Jonathan-0101/skeletonKey/Hardware/Symbols_Footprints_3D_Models/3D Models/DMG3415UQ-7.stp

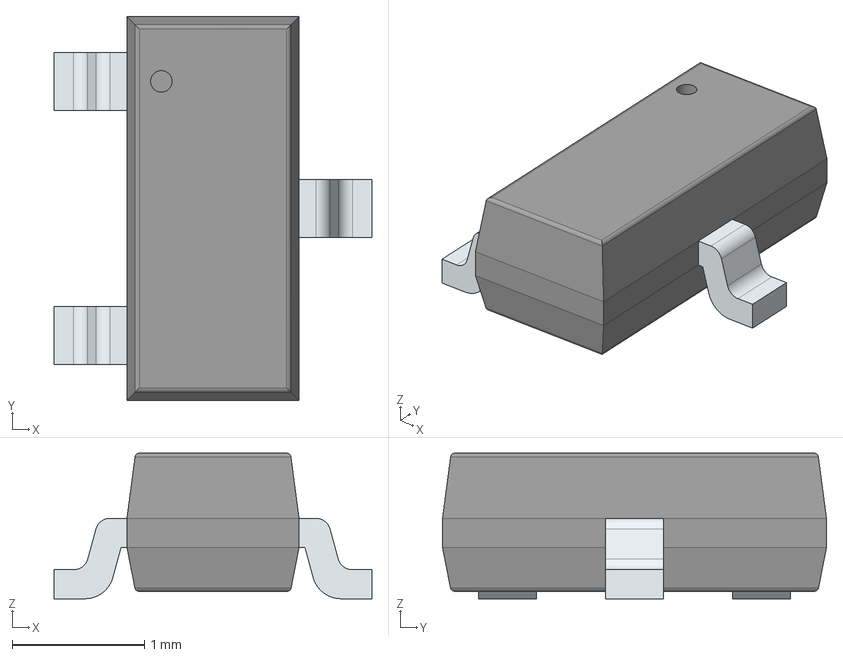
[picture p17: CAD file, 2025-07-19]
Hardware/Symbols_Footprints_3D_Models/3D Models/DMG3415UQ-7.stp
2.40 x 2.90 x 1.10 mm
PinsArrayL
FilletPinR
