Jonathan-0101/skeletonKey/Hardware/Symbols_Footprints_3D_Models/3D Models/C8051F330-GM.stp

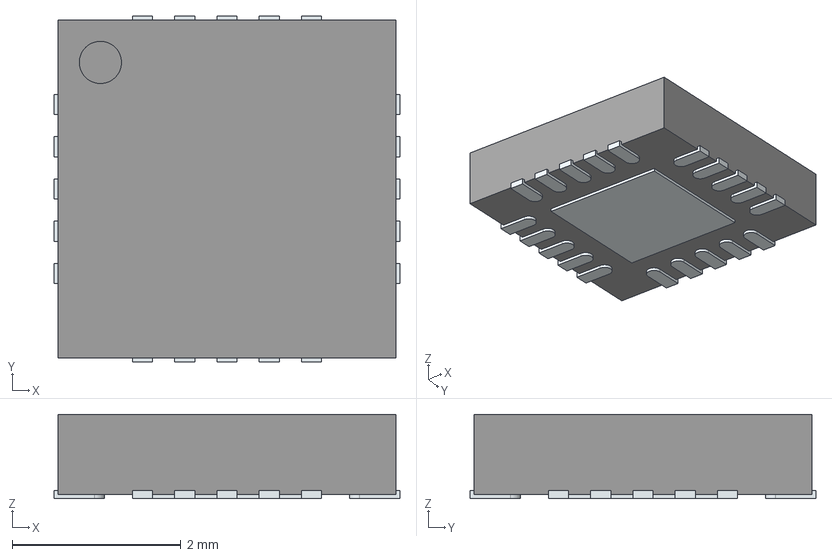
[picture p18: CAD file, 2025-07-19]
Hardware/Symbols_Footprints_3D_Models/3D Models/C8051F330-GM.stp
4.10 x 4.10 x 1.00 mm
ThermalPin
PinsArrayLR
PinsArrayTB
