Jonathan-0101/skeletonKey/Hardware/Symbols_Footprints_3D_Models/3D Models/B0310J50100AHF.stp

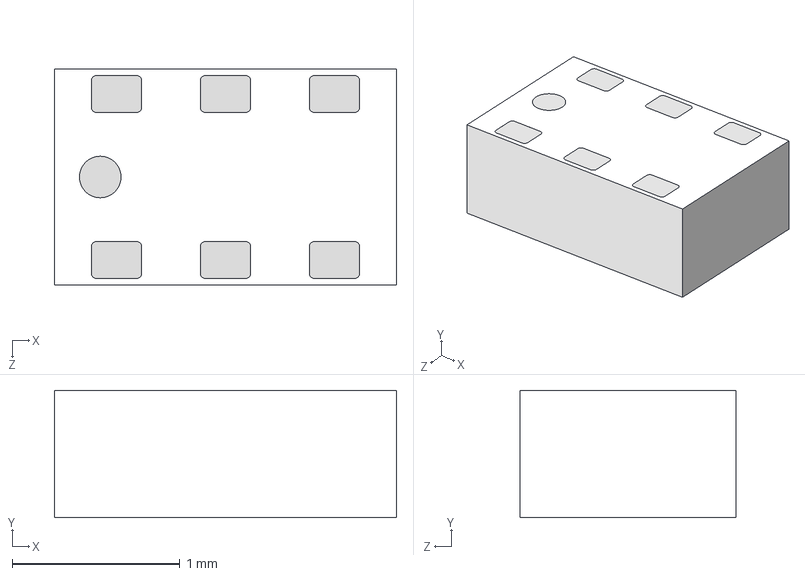
[picture p19: CAD file, 2025-07-19]
Hardware/Symbols_Footprints_3D_Models/3D Models/B0310J50100AHF.stp
2.04 x 0.76 x 1.29 mm
