Jonathan-0101/skeletonKey/Hardware/Symbols_Footprints_3D_Models/3D Models/PN5321A3HN_C106,55.stp

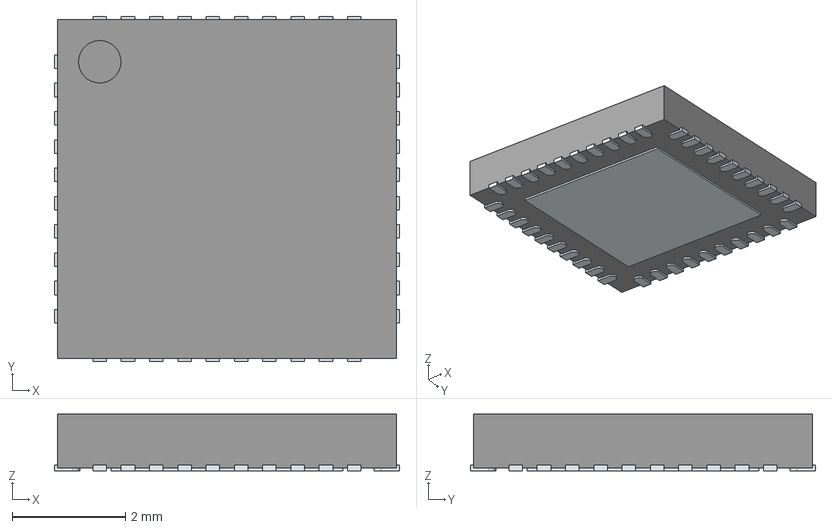
[picture p20: CAD file, 2025-07-19]
Hardware/Symbols_Footprints_3D_Models/3D Models/PN5321A3HN_C106,55.stp
6.10 x 6.10 x 1.00 mm
ThermalPin
PinsArrayLR
PinsArrayTB
