Jonathan-0101/skeletonKey/Hardware/Symbols_Footprints_3D_Models/3D Models/CC1101RGPR.stp

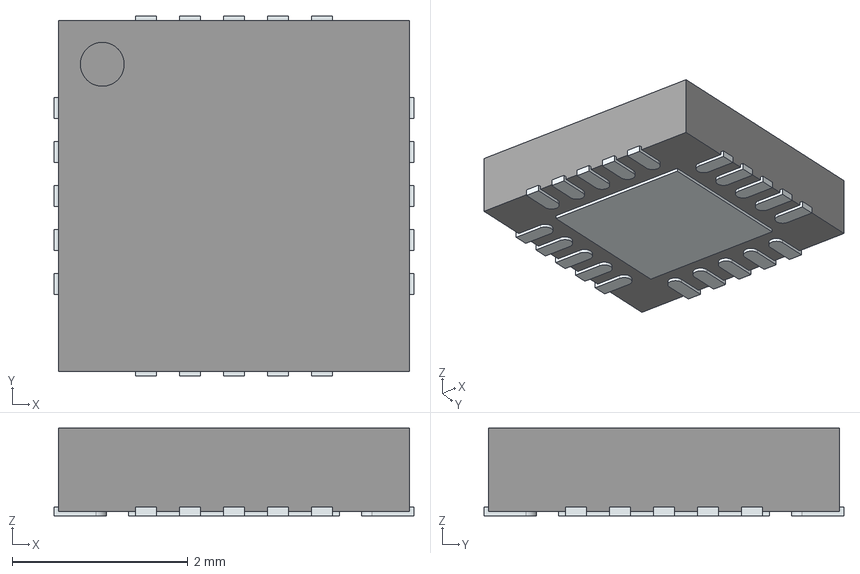
[picture p21: CAD file, 2025-07-19]
Hardware/Symbols_Footprints_3D_Models/3D Models/CC1101RGPR.stp
4.10 x 4.10 x 1.00 mm
ThermalPin
PinsArrayLR
PinsArrayTB
