Jonathan-0101/skeletonKey/Software/GUI/WiFiTools.h

// WiFiTools.h
#ifndef WIFITOOLS_H
#define WIFITOOLS_H

/**
 * @file WiFiTools.h
 * @author Jonathan Woolf
 * @brief Library for Wi-Fi attack tools
 * @version 1.0
 * @date 2025-03-04
 *
 * @copyright Copyright (c) 2025
 *
 */

#include <SD.h>
#include <WiFi.h>

#include <array>
#include <vector>

#include "esp_event.h"
#include "esp_event_loop.h"
#include "esp_log.h"
#include "esp_system.h"
#include "esp_wifi.h"
#include "esp_wifi_types.h"
#include "freertos/FreeRTOS.h"
#include "nvs_flash.h"

esp_err_t esp_wifi_set_channel(uint8_t primary, wifi_second_chan_t second);
esp_err_t esp_wifi_80211_tx(wifi_interface_t ifx, const void* buffer, int len, bool en_sys_seq);
esp_err_t esp_wifi_set_storage(wifi_storage_t storage);
esp_err_t esp_wifi_set_mode(wifi_mode_t mode);
esp_err_t esp_wifi_start();
esp_err_t esp_wifi_set_promiscuous(bool en);

/**
 * @brief Struct to store the MAC header of a Wi-Fi packet
 *
 */
typedef struct {
    unsigned frame_ctrl : 16;    /* frame control field      */
    unsigned duration_id : 16;   /* duration/ID field        */
    uint8_t addr1[6];            /* receiver address         */
    uint8_t addr2[6];            /* sender address           */
    uint8_t addr3[6];            /* filtering address        */
    unsigned sequence_ctrl : 16; /* sequence control field   */
    uint8_t addr4[6];            /* optional                 */
} wifi_ieee80211_mac_hdr_t;

/**
 * @brief Struct to store the payload of a Wi-Fi packet
 *
 */
typedef struct {
    wifi_ieee80211_mac_hdr_t hdr;
    uint8_t payload[0]; /* network data ended with 4 bytes csum (CRC32) */
} wifi_ieee80211_packet_t;

/**
 * @brief Struct to store the information of a 4-way handshake
 *
 */
typedef struct {
    uint8_t ap_mac[6];
    uint8_t sta_mac[6];
    uint8_t eapol[256];
    uint16_t eapol_len;
    uint8_t keymic[16];
    uint8_t replay_counter[8];
    uint8_t essid[64];
    uint8_t essid_len;
} HCCAPX;

typedef struct {
    uint8_t apMac[6];
    uint8_t staMac[6];
    uint8_t channel;
    uint8_t reasonCode;
    int deauthDelayMs;
} deauthPacket_t;

/**
 * @brief Enum to store the type of Wi-Fi packet to capture
 *
 */
typedef enum {
    HANDSHAKE_CAPTURE,
    CLIENT_DETECTION,
    NONE
} wifi_packet_flag;

/**
 * @brief Enum to store the type of Wi-Fi attack mode
 *
 */
typedef enum {
    DEAUTH,
    BEACON_SPAM,
    WiFi_IDLE
} wifi_attack_mode;

class WiFiTools {
   private:
    const bool wpa2 = true;
    char emptySSID[32];
    uint8_t channelIndex = 0;
    uint8_t macAddr[6];
    uint8_t randomMacAddr[6];
    uint8_t wifiChannel = 1;
    uint32_t currentTime = 0;
    uint32_t packetSize = 0;
    uint32_t packetCounter = 0;
    uint32_t attackTime = 0;
    uint32_t packetRateTime = 0;
    uint8_t targetBSSID[6];
    uint8_t targetChannel;
    wifi_packet_flag packetScanFlag;
    fs::SDFS* sd = nullptr;
    wifi_attack_mode attackMode = WiFi_IDLE;
    deauthPacket_t setDeauthPacket;
    long lastDeauthTime = 0;
    int lastBeconIndex = 0;
    long lastBeaconTime = 0;
    long beaconPaketDelayMs = 10;

    wifi_init_config_t cfg = WIFI_INIT_CONFIG_DEFAULT();
    std::vector<uint8_t*> detectedClients;
    std::vector<uint8_t*> capturedPackets;
    std::vector<wifi_ap_record_t> foundWiFiNetworks;

    /**
     * @brief Setup function for the beacon spam attack
     *
     */
    void beaconSpamSetup();

    /**
     * @brief Function to generate a random MAC address
     *
     */
    void generateRandomMac();

    /**
     * @brief Function to send a single beacon packet
     *
     */
    void sendBeaconPacket();

    /**
     * @brief Function to transmit a deatuthentication packet
     *
     * @param apMac MAC address of the access point
     * @param stMac MAC address of the device to deauthenticate
     * @param channel Chanel to transmit the packet on
     * @param reasonCode Reason code for the deauthentication
     */
    void sendDeauthPacket(uint8_t* apMac, uint8_t* stMac, uint8_t channel, uint8_t reasonCode);

    /**
     * @brief Function to identify clients based on detected packets
     *
     * @param hdr Pointer to the MAC header of the packet
     */
    void filterForClients(const wifi_ieee80211_mac_hdr_t* hdr);

    /**
     * @brief Function to filter packets for handshake capture
     *
     * @param buf Pointer to the packet buffer
     * @param type Type of the packet
     */
    void filterForHandshakes(void* buf, wifi_promiscuous_pkt_type_t type);

    /**
     * @brief Callback function for promiscuous packet handling
     *
     * @param buf Pointer to the packet buffer
     * @param type Type of the packet
     */
    static void promiscuousPacketHandler(void* buf, wifi_promiscuous_pkt_type_t type);

    /**
     * @brief Function to begin capture and processing of Wi-Fi data
     *
     * @param networkBSSID MAC address of the target network
     * @param channel Channel to capture packets on
     * @param captureTime The duration to capture packets for
     * @param captureHandshake Flag to capture handshake packets
     * @param detectClients Flag to identify connected clients
     */
    void processWiFiData(uint8_t* networkBSSID, uint8_t channel, int captureTime, bool captureHandshake, bool detectClients);

    // deauth frame definition
    uint8_t deauthPacket[26] = {
        /*  0 - 1  */ 0xA0, 0x00,                          // type, subtype c0: deauth (a0: disassociate)
        /*  2 - 3  */ 0x3A, 0x01,                          // duration
        /*  4 - 9  */ 0xFF, 0xFF, 0xFF, 0xFF, 0xFF, 0xFF,  // reciever (target)
        /* 10 - 15 */ 0xCC, 0xCC, 0xCC, 0xCC, 0xCC, 0xCC,  // source (ap)
        /* 16 - 21 */ 0xCC, 0xCC, 0xCC, 0xCC, 0xCC, 0xCC,  // BSSID (ap)
        /* 22 - 23 */ 0x00, 0x00,                          // fragment & squence number
        /* 24 - 25 */ 0x01, 0x00                           // reason code (1 = unspecified reason)
    };

    // beacon frame definition
    uint8_t beaconPacket[109] = {
        /*  0 - 3  */ 0x80, 0x00, 0x00, 0x00,              // Type/Subtype: management beacon frame
        /*  4 - 9  */ 0xFF, 0xFF, 0xFF, 0xFF, 0xFF, 0xFF,  // Destination: broadcast
        /* 10 - 15 */ 0x01, 0x02, 0x03, 0x04, 0x05, 0x06,  // Source
        /* 16 - 21 */ 0x01, 0x02, 0x03, 0x04, 0x05, 0x06,  // Source

        // Fixed parameters
        /* 22 - 23 */ 0x00, 0x00,                                      // Fragment & sequence number (will be done by the SDK)
        /* 24 - 31 */ 0x83, 0x51, 0xf7, 0x8f, 0x0f, 0x00, 0x00, 0x00,  // Timestamp
        /* 32 - 33 */ 0x64, 0x00,                                      // Interval: 0x64, 0x00 => every 100ms - 0xe8, 0x03 => every 1s
        /* 34 - 35 */ 0x31, 0x00,                                      // capabilities Information

        // Tagged parameters

        // SSID parameters
        /* 36 - 37 */ 0x00, 0x20,                                                                                                                                                                                      // Tag: Set SSID length, Tag length: 32
        /* 38 - 69 */ 0x20, 0x20, 0x20, 0x20, 0x20, 0x20, 0x20, 0x20, 0x20, 0x20, 0x20, 0x20, 0x20, 0x20, 0x20, 0x20, 0x20, 0x20, 0x20, 0x20, 0x20, 0x20, 0x20, 0x20, 0x20, 0x20, 0x20, 0x20, 0x20, 0x20, 0x20, 0x20,  // SSID

        // Supported Rates
        /* 70 - 71 */ 0x01, 0x08,  // Tag: Supported Rates, Tag length: 8
        /* 72 */ 0x82,             // 1(B)
        /* 73 */ 0x84,             // 2(B)
        /* 74 */ 0x8b,             // 5.5(B)
        /* 75 */ 0x96,             // 11(B)
        /* 76 */ 0x24,             // 18
        /* 77 */ 0x30,             // 24
        /* 78 */ 0x48,             // 36
        /* 79 */ 0x6c,             // 54

        // Current Channel
        /* 80 - 81 */ 0x03, 0x01,  // Channel set, length
        /* 82 */ 0x01,             // Current Channel

        // RSN information
        /*  83 -  84 */ 0x30, 0x18,
        /*  85 -  86 */ 0x01, 0x00,
        /*  87 -  90 */ 0x00, 0x0f, 0xac, 0x02,
        /*  91 - 100 */ 0x02, 0x00,
        /*  93 - 100 */ 0x00, 0x0f, 0xac, 0x04, 0x00, 0x0f, 0xac, 0x04, /*Fix: changed 0x02(TKIP) to 0x04(CCMP) is default. WPA2 with TKIP not supported by many devices*/
        /* 101 - 102 */ 0x01, 0x00,
        /* 103 - 106 */ 0x00, 0x0f, 0xac, 0x02,
        /* 107 - 108 */ 0x00, 0x00};

    // Rick Roll SSIDs
    const char* const rickRollSSIDs[8] PROGMEM = {
        "NeverGonnaGiveYouUp",
        "NeverGonnaLetYouDown",
        "NeverGonnaRunAround",
        "AndDesertYou",
        "NeverGonnaMakeYouCry",
        "NeverGonnaSayGoodbye",
        "NeverGonnaTellALie",
        "AndHurtYou"};

   public:
    /**
     * @brief Construct a new Wi-Fi Tools object
     *
     */
    WiFiTools();

    /**
     * @brief Initialise the Wi-Fi tools object
     *
     * @param sdInstance  Instance of the SD card filesystem
     */
    void initWiFiTools(fs::SDFS& sdInstance);

    /**
     * @brief Function to change the Wi-Fi channel
     *
     */
    void nextChannel();

    /**
     * @brief Function to run a Rick Roll beacon spam attack
     *
     * @param duration Duration of the attack in milliseconds, defaults to 15 seconds
     */
    void rickRollBeaconSpam(int duration);

    /**
     * @brief Function to scan for available Wi-Fi networks
     *
     */
    void scanWiFiNetworks();

    /**
     * @brief Get the Available Networks object
     *
     * @return std::vector<wifi_ap_record_t>
     */
    std::vector<wifi_ap_record_t> getAvailableNetworks();

    /**
     * @brief Function to clear the found Wi-Fi networks vector
     *
     */
    void clearFoundWiFiNetworks();

    /**
     * @brief Function to call from external code to run the action
     *
     */
    void runAction();

    /**
     * @brief Function to end the network deathentication attack
     *
     */
    void stopNetworkDeauth();

    /**
     * @brief Function to start a deauthentication attack
     *
     * @param networkSSID SSID of the target network
     * @param networkBSSID BSSID of the target network
     * @param channel Channel of the target network
     * @param availableNetworkIndex Index of the target network in the foundWiFiNetworks vector
     * @param targetMacAddr MAC address of the target device
     * @param delayMs Delay between sending deauthentication packets
     * @param reasonCode Reason code for the deauthentication
     */
    void startNetworkDeauth(uint8_t* networkSSID, uint8_t* networkBSSID, uint8_t channel, int availableNetworkIndex, uint8_t* targetMacAddr, int delayMs, uint8_t reasonCode);

    /**
     * @brief Function to run a deauthentication attack
     *
     * @param networkSSID SSID of the target network
     * @param networkBSSID BSSID of the target network
     * @param channel Channel of the target network
     * @param availableNetworkIndex Index of the target network in the foundWiFiNetworks vector
     * @param targetMacAddr MAC address of the target device
     * @param numPackets Number of deauthentication packets to send
     * @param delayMs Delay between sending deauthentication packets
     * @param reasonCode Reason code for the deauthentication
     */
    void deauthNetwork(uint8_t* networkSSID, uint8_t* networkBSSID, uint8_t channel, int availableNetworkIndex, uint8_t* targetMacAddr, int numPackets, int delayMs, uint8_t reasonCode);

    /**
     * @brief Function to initiate a passive handshake capture
     *
     * @param networkBSSID BSSID of the target network
     * @param channel Channel of the target network
     * @param availableNetworkIndex Index of the target network in the foundWiFiNetworks vector
     * @param captureTime Duration to capture packets for
     */
    void handshakeCapture(uint8_t* networkBSSID, uint8_t channel, int availableNetworkIndex, int captureTime);

    /**
     * @brief Function to initiate an active handshake capture
     *
     * @param networkBSSID BSSID of the target network
     * @param channel Channel of the target network
     * @param availableNetworkIndex Index of the target network in the foundWiFiNetworks vector
     * @param captureTime Duration to capture packets for
     */
    void activeHandshakeCapture(uint8_t* networkBSSID, uint8_t channel, int availableNetworkIndex, int captureTime);

    /**
     * @brief Function to identify clients connected to a network
     *
     * @param networkBSSID BSSID of the target network
     * @param channel Channel of the target network
     * @param availableNetworkIndex Index of the target network in the foundWiFiNetworks vector
     * @param captureTime Duration to scan for clients
     */
    void findClients(uint8_t* networkBSSID, uint8_t channel, int availableNetworkIndex, int captureTime);

    /**
     * @brief Function to toggle the Rick Roll beacon spam attack
     *
     * @param enable True to enable the attack, false to disable it
     */
    void toggleRickRollBeaconSpam(bool enable);
};

// Declare the global instance
extern WiFiTools* globalWiFiToolsInstance;

#endif  // WIFITOOLS_H
